eparadis/peg_board_adpaters/images/IMG_2506.jpeg

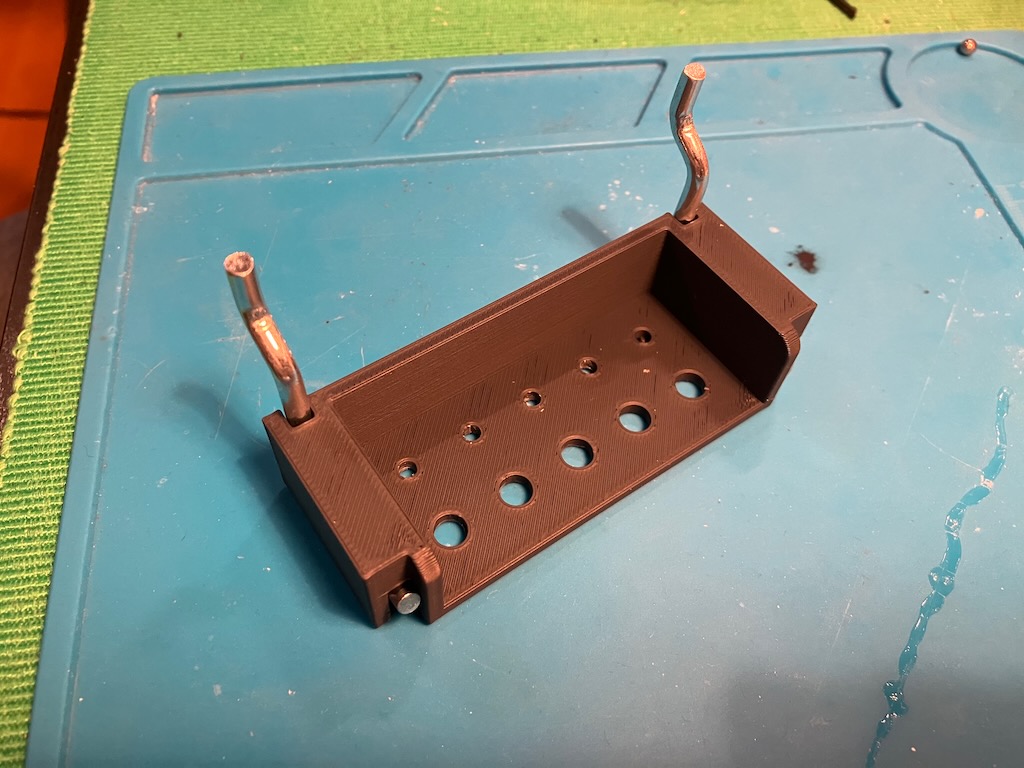
images/IMG_2506.jpeg
