eparadis/peg_board_adpaters/images/IMG_2509.jpeg

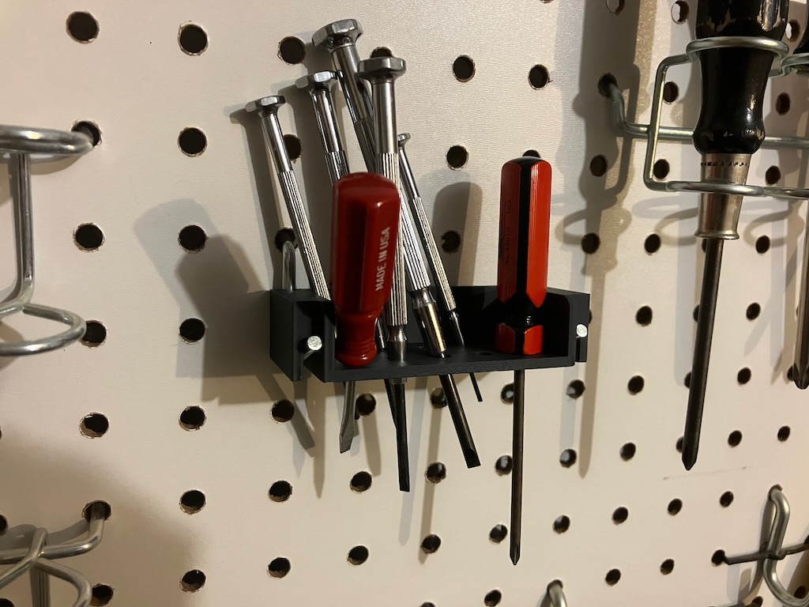
images/IMG_2509.jpeg
